tilestoolkit/tiles-hardware/Prototoype 2 RevA/Tiles_Proto2_scala4.pdf

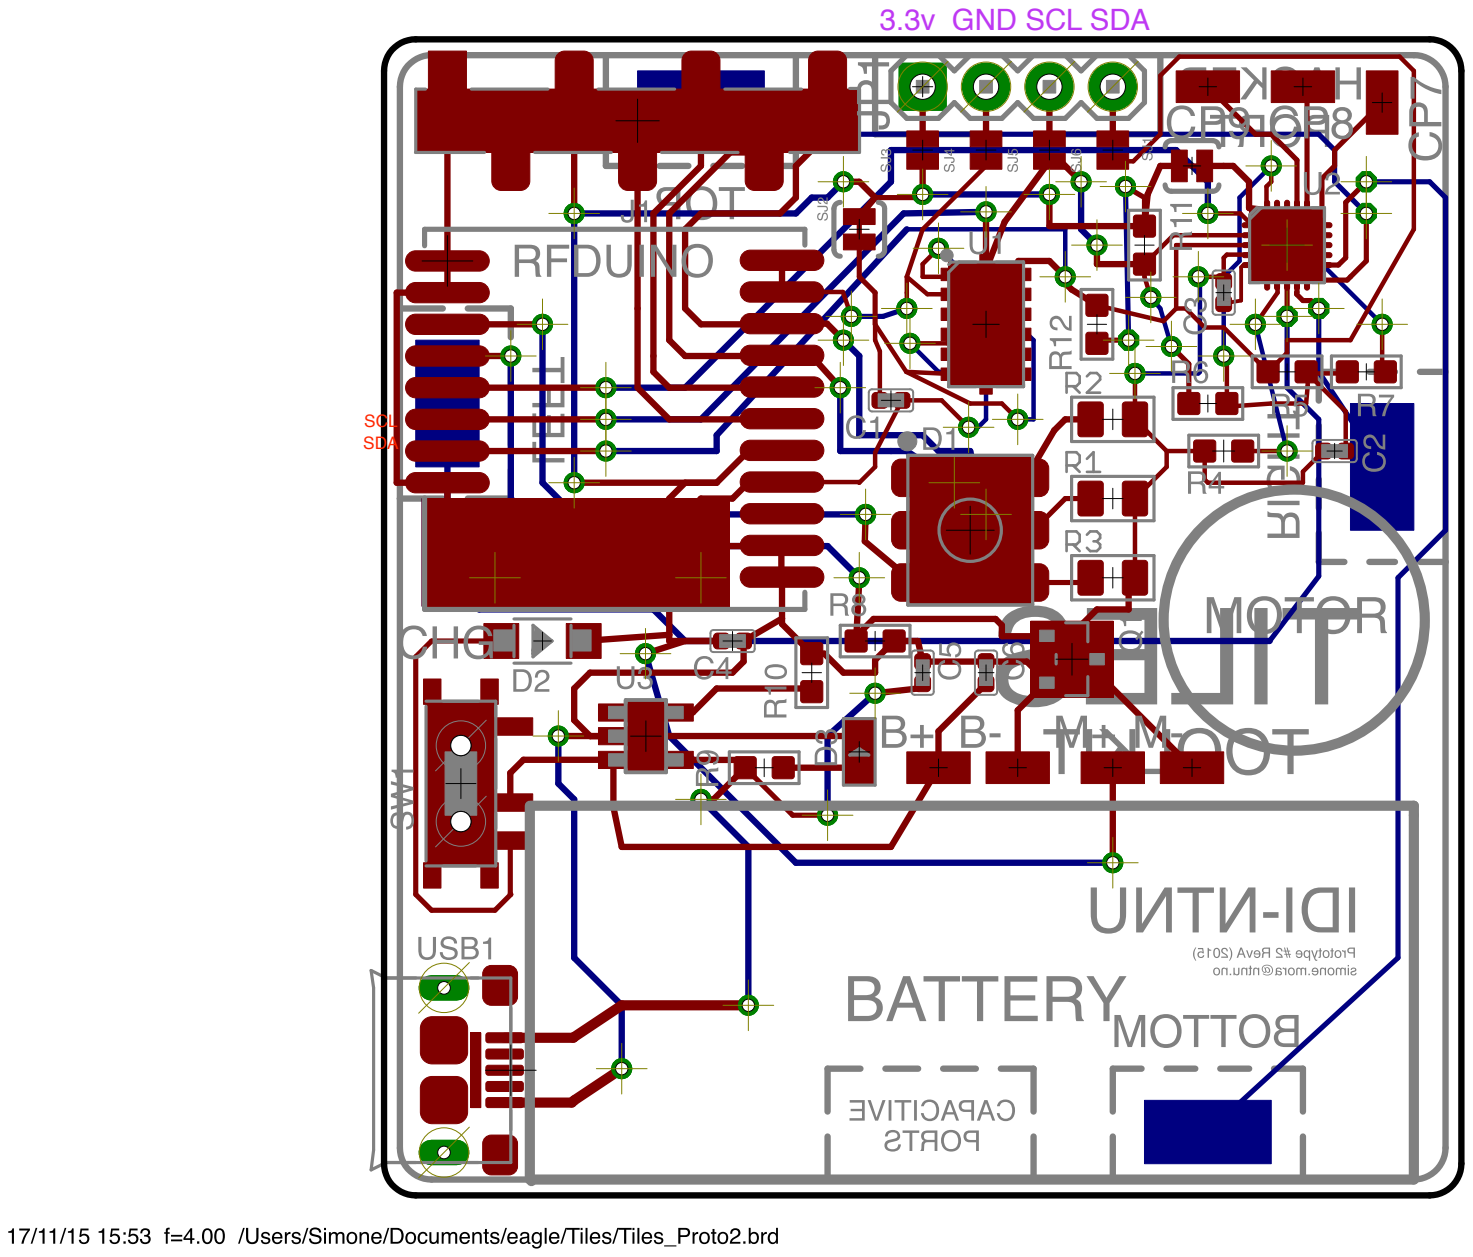
[picture p18: page 1]
