tilestoolkit/tiles-hardware/Prototoype 2 RevA/Tiles_Proto2_scala1.pdf

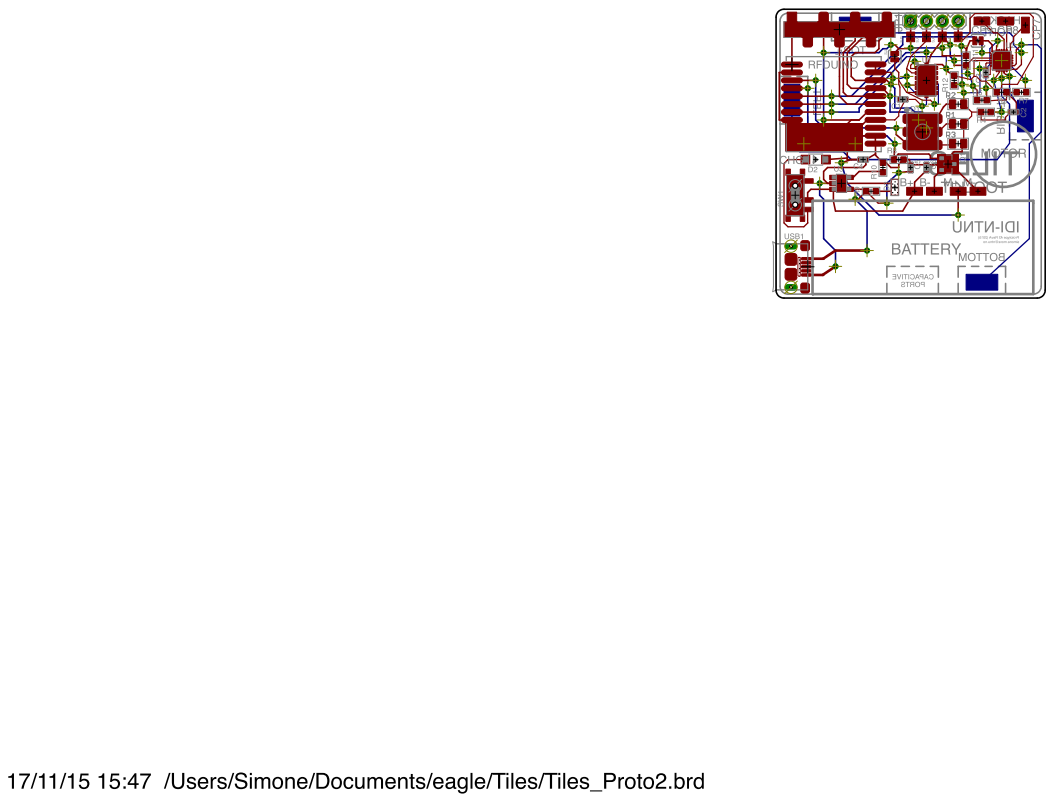
[picture p19: page 1]
