tilestoolkit/tiles-hardware/Prototoype 2 RevA/Tiles_Proto2_scala4_BOTTOM.pdf

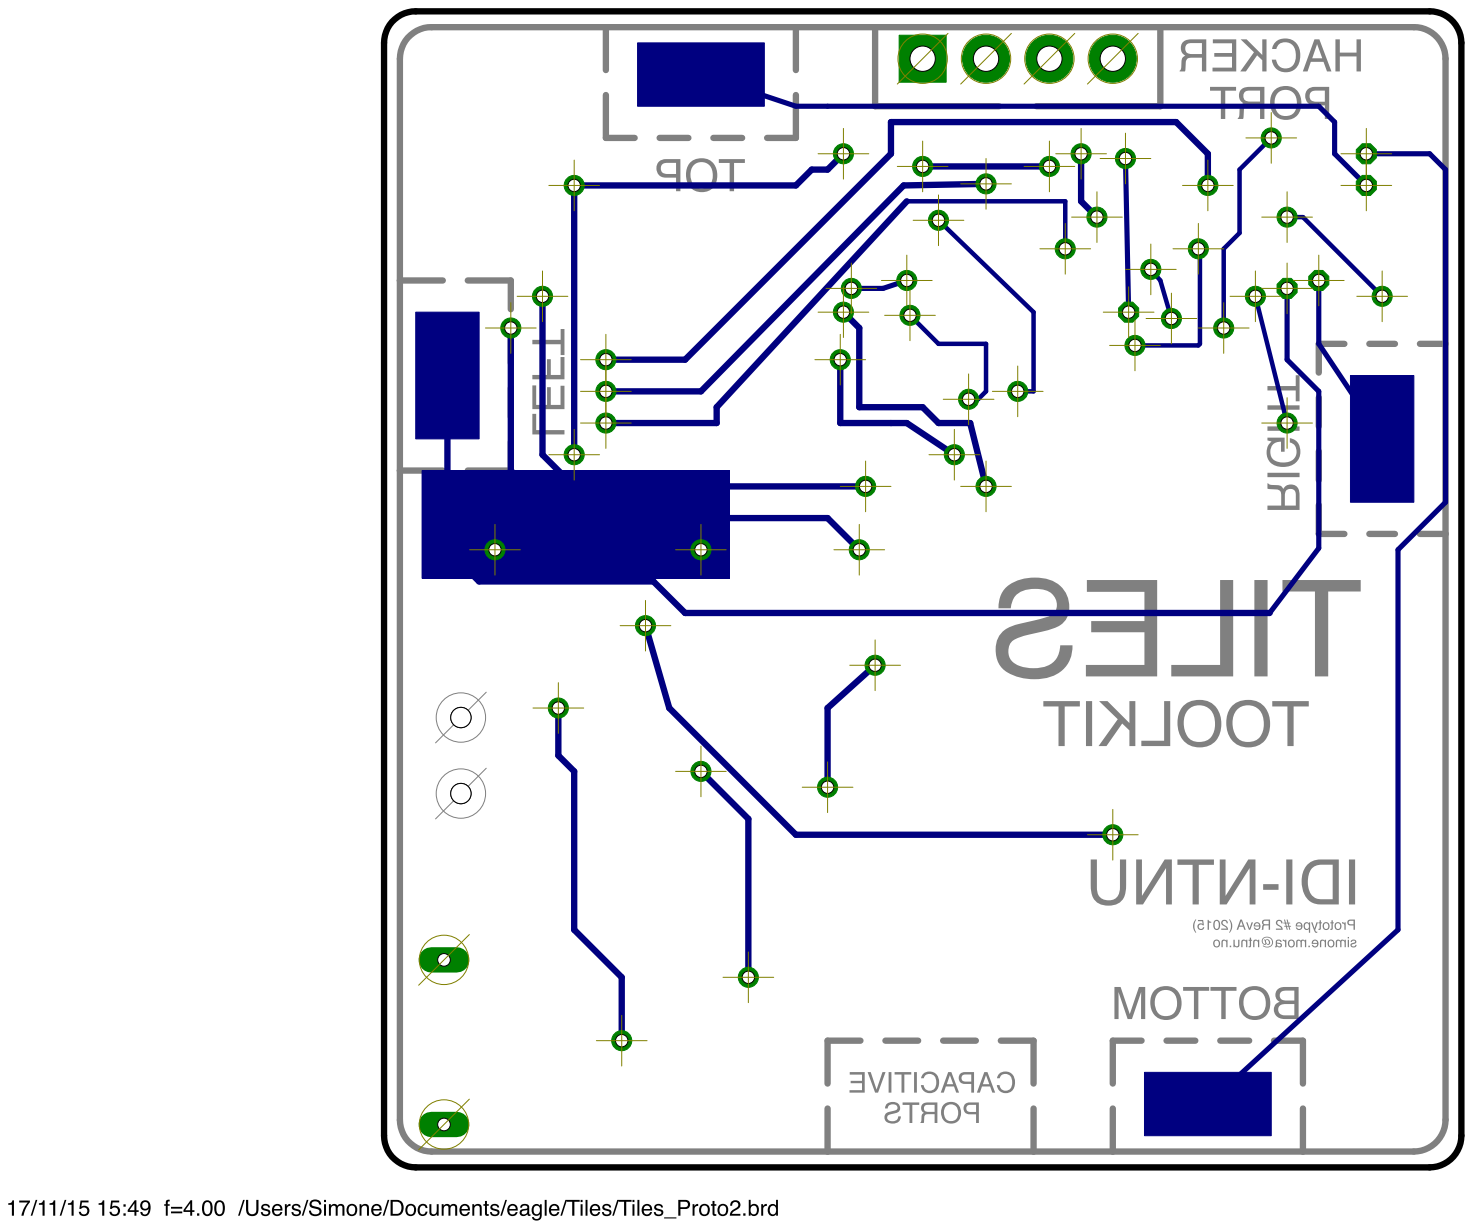
[picture p20: page 1]
