tilestoolkit/tiles-hardware/Prototoype 2 RevA/Tiles_Proto2_scala4_TOP.pdf

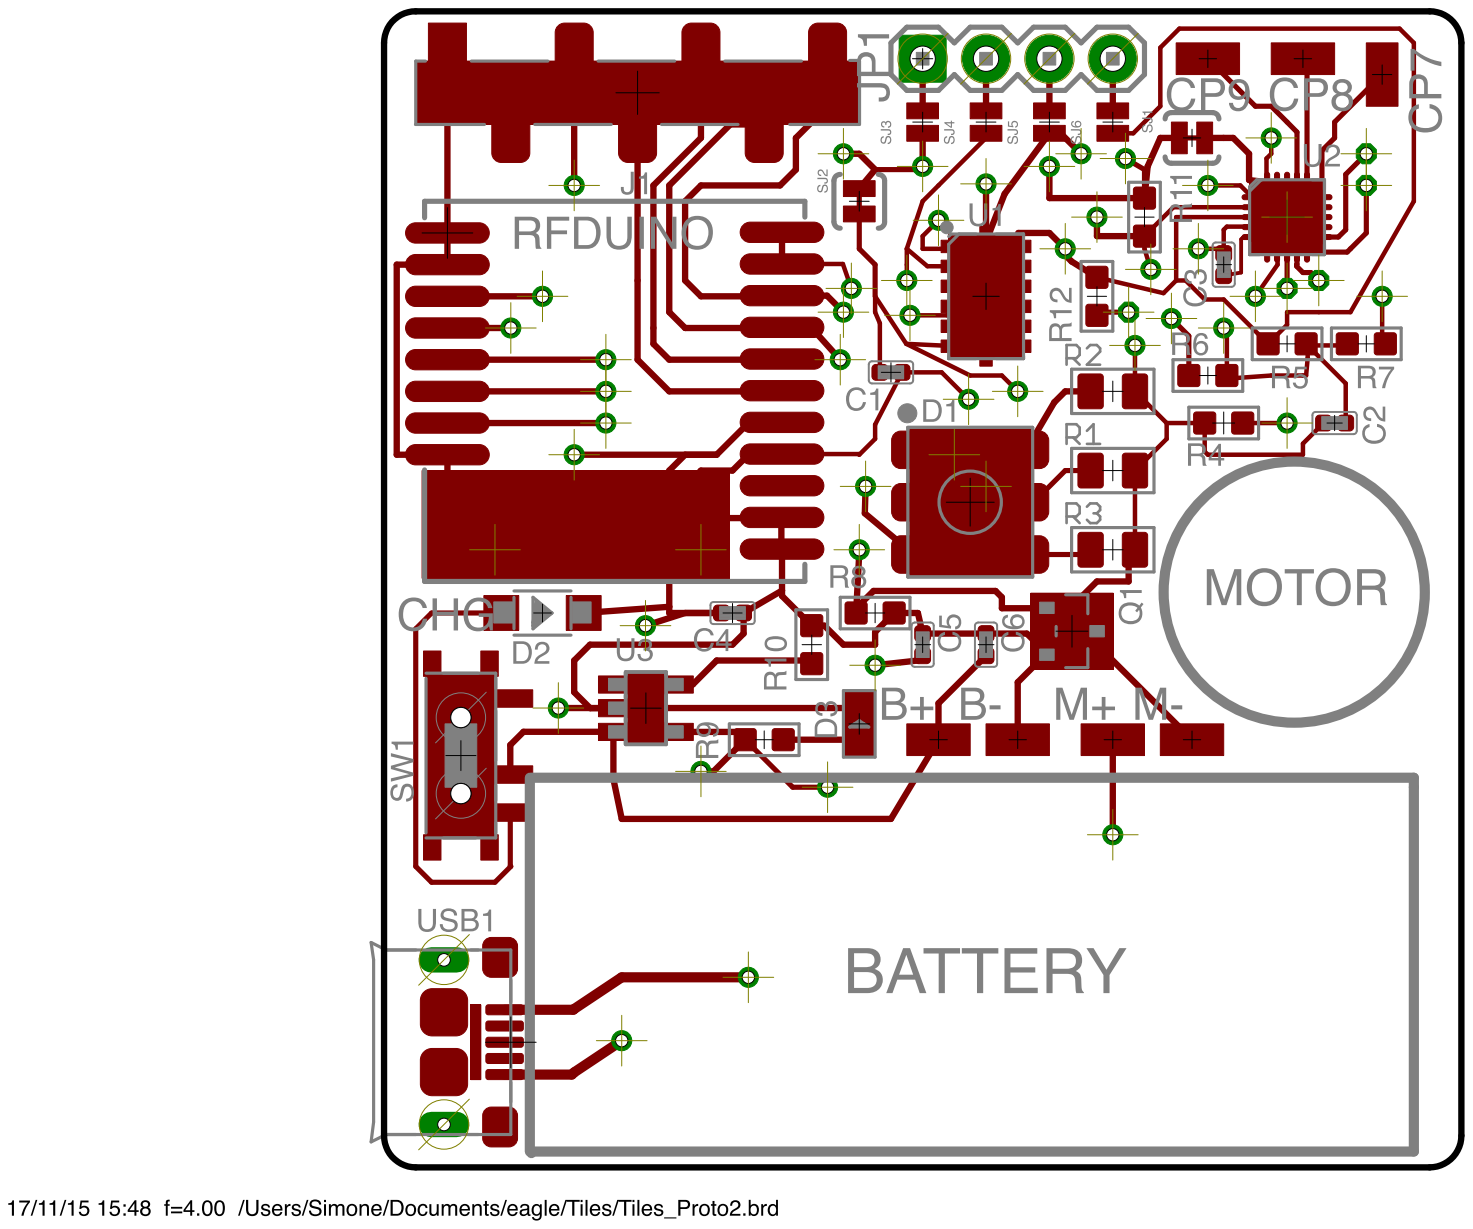
[picture p21: page 1]
